danstruthers/hydra-16/reborn/docs/status.md

# Status

Where HydraOS (the rebuild, released as 1.0 at parity) stands against the plan's phases
([design/reimplementation-from-scratch.md](design/reimplementation-from-scratch.md), Part III), what the
spikes measured, and what measuring changed.  HyForth's, from step 6.6 on: [forth-status.md](forth-status.md).
The documentation (the plan's 19.4, written after the review of October 2026): [hydra-16.md](hydra-16.md), the guide
to the whole system, hardware and software (and `hydra-16.pdf`, the guide, the tutorial, the guides, the programmer's guide and the hardware reference as one book, to print);
[tutorial.md](tutorial.md), the first hour; [using/](using/README.md), the guides (rc, the tools, HyForth, hylang, BASIC); [programming/](programming/README.md),
the programmer's guide (calls, memory, tasks and notes, files and namespaces, servers and drivers, modules, video).
BASIC's design: [basic.md](basic.md).

## In short

HydraOS 1.0 is the parity release (October 2026: the user's word, on the emulator's evidence; the board's day of use is to come), the old system frozen in `old/` beside it.  Phases 0 to 2 and 4 to 7 are done, and phase 9's three tools; phase 3 (storage) is done but for the progress a long format or check shows, and phase 8 (the Vera X) but for its rest (8.8); phase 10 (the X16 migration utility) waits for the end.  Phase 4 (programs) is its loader, rc, the core tools, the assembly SDK, the C target and `ed`;
phase 5 (the remaining devices) is sound, the song player, GPIO and I2C, the clock, `/pc`, `xmodem`, and `/proc`'s files for a task's memory and state; phase 6 (HyForth) is `forth`, a Forth 2012 system (Core, Core Extension, Exception, Facility, File Access, Programming-Tools, Search-Order and String) that passes the Forth 2012 test suite's tests of them, with a `sys-` word for each system call a program makes (made from the specification), `SH`, `RUN`, banks and segments, Ctrl-C, libraries from `/lib/forth` and scripts (`forth file.fs`, `#!/bin/forth`); its ROM core is the Core word set, and the other word sets are pre-compiled libraries it loads into its dictionary (`/lib/forth/startup.fs` names those it starts with), and the login shell (`forth -l`: the ROM's `/lib/shell`).  Phase 7 (hylang) was done twice: the first hylang (7.1 to 7.4a, its library modules and its built-ins partially applied, to commit `a0973eb`) was deleted after a review of danlang and of it.  danlang, the reference, was fixed first (its 22 bugs, its quirks, one rule for each inconsistency, its shorthand made seven prefixes and `[...]`, callable hashes, text as bytes, one argument convention for its built-ins, and `reference.md`, its specification), and hylang was written again from scratch to the plan the review led to (`docs/hylang.md`): danlang's suite passes, the Hydra's layers are there (its built-ins, a `sys-` function for every call, the device libraries, hylang as a shell), and a bytecode machine and native code make it 1.9 times HyForth's time over twenty benchmarks.  Beyond the plan, BASIC: first EhyBASIC (Microsoft BASIC 2A) as a program, now a structured BASIC of the system's own in its place, in QuickBASIC's way on the Hydra's exact numbers (compiled whole into a stack machine's code; procedures, records, files, sound, graphics, system calls, a prompt that keeps a program, and a shell mode, `basic -l`).  The kernel boots in the emulator, runs POST (with the old
hardware test a key away), starts its modules from the paged ROM in tasks of their own, schedules them
preemptively, runs calls between tasks and copies between them, takes every interrupt through one path, manages
task RAM, banks and shared segments, and delivers notes.  The file layer is in: fds, channels, requests to
servers, servers built on srvlib, waits that a server's interrupt can end for a few cycles; and namespaces, Plan 9's:
binds, mounts, unions and union directories, a current directory, shared by a task's children till they change
them.  The console driver (`cons`, task F) serves `#c`: windows, Plan 9's way (rio's, on the serial terminal: a
console each, shown with Ctrl-] and a digit; each window's screen kept in the console driver's RAM banks, written
by a VT100 and painted from: the text windows' W1), lines edited at the console, raw keys,
Ctrl-C and Ctrl-\ to the shown window's note group, and paced sending up to 115200.  The kernel's own devices are a driver of
their own (`kdev`): the root's mount points, null and zero, the kernel's messages (`/dev/kmesg`: what it printed on the
bring-up console, the boot's too, its last 4K, kept in the kernel task's RAM), the ticks, the modules, the tasks, pipes, and the
environment.  The storage driver (`storage`, task E) owns the SPI bus and the disks: `#S` (the SPI devices), `#d`
(SD cards, through a cache of their blocks; the ROM disk; the RAM disks), and HydraFS on them (`#f`, the old
system's, ported: the module's second bank).  The paged ROM holds the ROM disk's volume after the modules (`/rom`:
`romfs/`).  init starts the RAM disks, builds its namespace from `/rom/lib/namespace`, and runs the login shell (`/lib/shell`'s:
HyForth, `forth -l`; rc without one) in window 0 and in each window the user asks for (Ctrl-] c); each shell builds
its own namespace from the same file as it starts (Plan 9's `newns`), with its own area of the RAM disk at `/ram`,
then runs its profile (rc's `/rom/lib/profile`, HyForth's `/lib/forth/profile.fs`).  `SPAWN` takes a
path through the namespace: a module of the paged ROM (`#m`'s files, at `/bin` by `#m/bin`) runs in place, and a
program in a file (a RAM program: `sdk/asm/hyx2.cfg`) is read into its task's RAM at `$0800` by the task itself as
it starts.  rc is Plan 9's (lists, quoting, `if`, `for`, `while`, `switch`, functions, redirections, pipelines,
background tasks, `$status`, globbing, `rc -c`), with the core tools beside it: files (`ls -l`, `cp -r`, `mv`,
`rm -r`, `du`, `df` ...), text (`wc`, `head`, `tail`, `uniq`, `xd`, `more` ...), tasks (`ps`, `kill`, `top`, `ns`
...), and the disks' (`mkfs`, `fsck`, `label`: RAM programs on the ROM disk, at `/bin` too).  Programs are written in
assembly (`sdk/asm`) or in C (`sdk/c`: cc65, with a library of the Hydra's own under the standard one: files,
buffered stdio, the environment, `system`, `signal` over notes, conio on the console's raw mode); `grep` and
`sort` are C programs.  `ed` is the old system's line editor, a program now (`edit` till phase 9's screen editor took the name).  The sound driver (`snd`, task C) serves the
YM2151 at `#a` (`/dev/snd`, `sndctl`, `bell`), with the old system's library (patches, notes, volumes, drums,
claims), and `sndctl` takes each channel's command as text, so rc makes sound; the console rings its bell; `play`
plays songs (the X16's ZSM files, on the ROM disk at `/rom/songs`) and scores (the score language, compiled as they
play), and a line of it (`play -m`) for each language's `snd-mml` and BASIC's `PLAY`.  The VIA's port A is `/dev/gpio` (its
pins, CA1 and CA2) and `/dev/i2c` (the I2C bus on two of its pins).  The clock is set from the DS1747 as the
system starts, if there's one: `/dev/time`, and `date`.  A folder on the PC is `/pc` (`#P`, the console driver's),
served over the serial line by the PC tool (`sim/tools/hydrapc.js`, which is the terminal too); `xmodem` sends
and receives a file with any terminal program.  `/proc/N` has a task's memory as files (`mem`, its 64K as it sees it,
and `ram`, its banks), its registers (`regs`), its environment (`env`), and a file to send it a note (`note`).
Phase 8 is the Vera X (the X16's VERA in slot 0: the user's is Joe Burks's VERA X, the X16 gateware):
the emulator has one (`sim/lib/vera.js`, `run.js --vera`, a live view in a browser), a driver serves it (`vid`: `#v`,
`/dev/vid`'s `ctl`, `term`, `vram`, `pal`, `sprites`, `font`, `frame` and `psg`, and claims for a program that
writes the chip itself), the console's windows are shown on its screen as well as the serial terminal (consctl's
`screen`, `serial`, `both`), its PSG is sound channels 8-23 (`/dev/snd`'s, `/dev/sndctl`'s `wave`,
`/dev/psg`; `play` plays a ZSM's PSG part), and its PCM plays samples (`/dev/vid/pcm` and `pcmctl`; `play`
plays WAV files and a ZSM's PCM instruments); the emulator plays its sound (`run.js --sound`, `--wav`); its keyboard
and mouse are its input controller's, the X16's SMC (the `input` program types the keys into the console, and the
mouse is `/dev/vid/mouse`, a sprite its pointer); the driver draws on its bitmap (`/dev/vid/draw`), with the same
words in each language (HyForth's `lib video`, hylang's `video`, C's `vera.h`, cc65's TGI); its SD card is a disk (`/sd/v`); the carrier card is
still to come (8.8).
Phase 9's tools are done: the debugger, `db` (`/rom/bin`, in C), starts a program stopped or stops a task, steps it an
instruction at a time (the kernel's `TASKSTEP`, behind `/proc/N/ctl`), runs it to breakpoints, and shows its
registers, code and memory with ld65's symbols; `edit` is a screen editor, nano's way, its text in RAM banks
(the old line editor is `ed` now); and `as` assembles ca65's language on the Hydra itself, the SDK's include files
in `/lib/as`, into the same program ca65 and ld65 make.

```
PASS boot    the kernel boots, POST finds nothing wrong; init runs hello and waits for it  (0 checks, 7.2M cycles)
PASS init    init from files (rc the shell, a card's /lib/shell naming it): the RAM disks started, the namespace file run, each shell's own namespace and /ram (a window's too); the shared RAM disk stopped, /bin's union still there  (0 checks, 32.0M cycles)
PASS newns   the default namespace's library (nslib): an old area emptied, a namespace file run (quotes, comments, $task, flags, bad lines)  (13 checks, 8.0M cycles)
PASS post-t  POST: a T line stuck low (U7)  (0 checks, 0.8M cycles)
PASS post-zp POST: only the zero page and stack per task (a decoding fault)  (0 checks, 0.8M cycles)
PASS post-ram POST: an address line of RAM module 1 stuck low; the module is left unused  (0 checks, 1.0M cycles)
PASS post-sh POST: no shared RAM  (0 checks, 1.0M cycles)
PASS hwtest  a T typed during POST starts the hardware test (paged ROM bank 1)  (0 checks, 1.0M cycles)
PASS hwtool  hwtest at rc: the system starts again (REBOOT), and POST takes REBOOT_HWTEST's word as a T  (0 checks, 12.6M cycles)
PASS task    tasks and the scheduler: SPAWN, EXITS, WAIT, SLEEP, preemption, PAUSE and WAKE, orphans  (29 checks, 8.2M cycles)
PASS note    notes: the defaults, handlers, a note to oneself, WAIT ended by one, note groups  (29 checks, 7.2M cycles)
PASS file    files and servers: OPEN, READ, WRITE, SEEK, STAT, DUP; text, ctl, data, directories; waiting  (54 checks, 10.0M cycles)
PASS ns      namespaces: BIND, MOUNT, UNMOUNT, unions and union directories, CHDIR, clean names, inheritance  (45 checks, 21.2M cycles)
PASS dev     the kernel's devices (kdev): #/, #n, #t, #m, #p; pipes; a union keeping what was there  (42 checks, 8.8M cycles)
PASS proc    /proc/N's mem (its RAM, bank, ROMs, the I/O area), ram (its banks), regs, env, note and fd (FD2PATH, TR_FD); ctl's stop and start; the kernel task's and a driver's refused  (46 checks, 9.4M cycles)
PASS forth   HyForth (Forth 2012): the test suite (Core, Core Extension, Double-Number, Exception, Facility, File Access, Locals, Memory-Allocation, Programming-Tools, Search-Order, String, Block) in three sessions, its files INCLUDED from a card, the word sets' libraries REQUIREd from /lib/forth; scripts (forth file.fs, #!/bin/forth: arguments, REQUIRE from /lib/forth, a library, an error, a pipeline, code banks); at the console: startup.fs's Programming-Tools (.S), libraries REQUIREd (and again after a MARKER), a definition, KEY? and KEY, errors (a file's, the system's), SH, RUN, a sys- word, a bank, the constants library, Ctrl-C, BYE  (3 checks, 513.8M cycles)
PASS basic   BASIC (docs/using/basic.md) at the console: its prompt, PRINT, exact numbers, keywords in either case, a program typed by its line numbers (LIST, RUN; GOSUB, DATA, READ, INPUT, DIM, a FUNCTION), Ctrl-C (Break in) in a GOTO's loop and CONT, INKEY$'s key, errors (at the prompt; a typed program's by its line's number), BYE (code 0); a pipeline into it (no prompt; an error's line ended, its end at stdin's); in /ram: SAVE, LOAD, RUN "name", a file not there (by its name), the text cat; scripts (basic file, #!/bin/basic: status 0 and 1, a file not there); files: OPEN's modes, PRINT #, INPUT #, LINE INPUT #, EOF, APPEND, CLOSE, the cat; a file not open, open, not there; INPUT's Redo from start; sound: SOUND's notes (a patch, a volume, off), SLEEP between them (timed), BEEP (the bell), a line for /dev/sndctl (the volume kept; the driver's error), a channel past 23, a patch past 127; SYS: calls by name (GETPID, TICKS, BANKS_ALLOC; one not there) and RREG; memory: FRE, an array of 10001, 301 strings; the shell (basic -l at rc's prompt): BASIC's lines and rc's by the rule, cd and the prompt, $status, %, a usage, ENV$, a program line, exit  (3 checks, 132.2M cycles)
PASS bsuite  BASIC's suite (tests/basic, docs/using/basic.md), from a card: programs that check themselves, each its checks and none failed (arithmetic: the operators and their order, exact numbers, complex numbers, literals: E notation, &H, the # forms, .5; suffixes; a base; the number functions: exact when they can be, else DIGITS digits, RND, fractions' and complex numbers' parts, GCD, FIB, shifts, VAL, STR$ in a base, MKN$; comparisons, the bitwise operators on big integers, IF's forms, SELECT CASE; strings: their functions, MID$ =, fixed lengths, past 255, the garbage collector; arrays: TO, dimensions, used before DIM, REDIM PRESERVE, ERASE, LBOUND, SWAP; FOR's exact steps, DO, WHILE, EXIT, GOTO, GOSUB, RETURN label, ON, line numbers, _; SUBs and FUNCTIONs: by reference and by value, recursion, STATIC, SHARED, CONST, a call among a call's arguments, one calling another, INCLUDE; TYPE: nested records, arrays of them, copies, a field by reference; DATA, READ, RESTORE, CONST, OPTION BASE, DEFSTR; ON ERROR, RESUME's forms, ERR, ERL, ERR$, the system's errors; files: OPEN's modes, PRINT #, WRITE #, INPUT #, LINE INPUT #, INPUT$, LOF, LOC, SEEK, GET, PUT, FREEFILE, directories; the Hydra's: SYS and RREG, a bank of its own, machine code, FRE, SLEEP, TIMER, DATE$, TIME$, ENV$, ARG$, COMMAND$, SHELL, SHELL$, STATUS; inline assembly: ASM blocks, CALL ASM's labels and registers, the program's variables and CONSTs by name, data, a block in a SUB, a later block's label, a macro, .if, cheap and unnamed labels, .include and a system call, the blocks' own bank and .bss); scripts piped into basic, their output tests/basic's: the errors' messages (at the prompt, a typed program's by its line numbers; ASM's: the assembler's at its line, a label not there, a block not ended, past 8K, ASM at the prompt; CALL ASM at the prompt), PRINT's layout (zones, TAB, SPC, POS, numbers' forms, PRINT USING's pictures and {} fields, WRITE, a base), the prompt (lines typed, replaced, taken out; LIST's ranges, labels; DELETE, CLEAR, SAVE, LOAD, RUN "f", STOP, CONT, SYSTEM), INPUT's answers (Redo from start, quotes, an empty line, LINE INPUT, INPUT ;)  (3 checks, 256.0M cycles)
PASS hyforth HyForth's additions (docs/hyforth.md): names in lower case; words (each word's xt, and whether it's a literal, immediate, assembly or Forth); the libraries loaded (libs), one not searched (-lib) and searched again (lib, where it was), the one with lib refused, a .fs one, one a MARKER takes out; disasm (the modes, the Rockwell opcodes, a jsr to a word), see of a code word (with disasm.fl, and without), sys, the bit words, random's numbers; the terminal's sequences, form, ekey and the keys (an arrow key, a character); the sound words (notes on the YM2151, a claim, the volume; a channel's level, its old name; the registers read back: a note's key code and fraction; a song by play, its error; a note by its frequency, a glide, the LFO, a channel's sensitivity, the noise; a line of MML and a chord, by play); ctl (and its error); compile-only words typed (THROW -14: >r, if, .", a synonym of one, a library's) and compiled  (3 checks, 172.0M cycles)
PASS fshell  HyForth as a shell (forth -l, shell.fl): its namespace and profile; a line Forth's or rc's by its first word (a number, a word, a pipeline, a redirection), or rc's by % (a program a word shadows); cd and the prompt (its format); a definition over lines (the second prompt); status and $status; & ($apid) and wait; programs as values: sh-out, output-of, a word's output a program's input (|, piped: one that ends first, Ctrl-C), spawn; Ctrl-C ending a program; errors, a usage; -lib shell and lib shell; exit  (3 checks, 74.8M cycles)
PASS fhydra  HyForth's Hydra words (hylang's layer 2): argc under forth -l (0: -l isn't an argument); a directory read (open-dir, read-dir, close-dir), =mkdir, get-dir and set-dir (the prompt follows), ior>text; setenv, getenv, unsetenv; a note to itself taken by on-note's handler, between words and in a loop, and one it says no to (as Ctrl-C); pause  (3 checks, 34.6M cycles)
PASS fdev    HyForth's device libraries (hylang's layer 3, source over the devices' files): gpio (pins, the port, ctl, CA1's edge), i2c (a memory written and read at a register, the devices), spi (an echo device's transactions, mode 3), cons (the window, the windows), proc (a task's args, cwd, regs, memory), clock (the chip, the time set), disk (a disk's ctl, the cards: one on SPI device 5), pc (the PC tool answers; a file of its read), and sound's note-of and tune (its notes on the YM2151, in time)  (3 checks, 231.0M cycles)
PASS findex  HyForth's index of the word lists (a bank's chains by a name's hash): a word redefined, a definition hidden till ;, a MARKER's words gone, MARKERs till the bank's full (started again), more word lists than records, EVALUATE of a bank's text (no index), the index's bank overwritten (started again); 500 searches of a name that isn't there in under 150 ticks (620 without the index)  (3 checks, 37.2M cycles)
PASS wcache  HydraFS's walk cache (the names looked up, there or not, and the directories' entries on the way): a name not there, then made, renamed, removed; directories made, removed, renamed under a name looked up; a name made through /lib's union after it wasn't there; each looked up again as it is now  (3 checks, 35.6M cycles)
PASS fload   HyForth loading a file: its read-ahead (a CR LF across its 512-byte buffers, CR LF and CR line ends, a line of 130 cut at 128, a last line ended by a CR and the file's end), names between tabs, numbers with each prefix, in base 36, a double; hydra.fs REQUIREd in under 300 ticks (383 before 6.20)  (3 checks, 25.2M cycles)
PASS fnumbers HyForth's numbers (numbers.fl, on the numbers and math libraries): numberstest.fth, each number word checked as the test suite checks (tester.fr's T{ ... -> ... }T): literals of every kind (and cells and doubles Forth's still), compiled with code banks and without, the number stack, the arithmetic, the tests, the conversions, the bits, text in the base and in others (set-base: cells read and shown by the library), the math functions, digits, the errors, nvariable, nconstant, nvalue; then n., n.base, n.s, nformat and cells in bases that aren't a radix, typed  (3 checks, 28.8M cycles)
PASS lshell  the shell /lib/shell names (the ROM's: /bin/forth -l, HyForth the login shell): init's in window 0, wstart's in a window made (Ctrl-] c: $window); send, a line typed in another window (#cN/kbdin), run there, then one longer than its keys' queue (the write waiting for room)  (0 checks, 29.8M cycles)
PASS spi     SPI and #S (storage): transactions, kept bytes, modes 0 and 3, one open at a time, the time a byte takes  (43 checks, 8.2M cycles)
PASS disk    the disks (storage): #d, the ROM disk, SD cards (SDHC and SDSC), RAM disks, their ctl files, the time a byte takes  (67 checks, 16.0M cycles)
PASS fs      HydraFS (#f): files and directories, create, write, holes, remove, rename, a length, format, label, check, old cards, mounts  (92 checks, 66.2M cycles)
PASS rom     the ROM disk: /rom (#f, spec x) walked on the Hydra, every file read back against its source (romfs/romfs.txt)  (2 checks, 285.6M cycles)
PASS load    SPAWN by path and the loader: modules in place (#m/bin), RAM programs from a card (arguments, fd maps), errors  (49 checks, 28.2M cycles)
PASS env     environments: ENV_GET, ENV_PUT, ENV_DEL, ENV_NAME, a child's copy, #e (/env) as files  (62 checks, 13.2M cycles)
PASS kmesg   the kernel's messages: KMESG (the boot's banner first, at offsets, the ring full: its last KMESG_SIZE) and /dev/kmesg (kdev's #n/kmesg) read in parts  (12 checks, 21.2M cycles)
PASS rc      rc: quoting, lists, redirections, pipelines, if, for, while, switch, functions, globs, scripts, Ctrl-C, its start  (3 checks, 87.8M cycles)
PASS tools   the core tools at rc: files, text, tasks, the disks' (/rom/bin); /proc's args, cwd, ns; the SDK's samples  (3 checks, 156.0M cycles)
PASS c       the C target (cc65): its samples at rc, the library's test (ctest), conio's raw keys (an Escape alone too; and raw ended with the program)  (81 checks, 89.4M cycles)
PASS cnum    the numbers in C and assembly: num.h's test (ntest: the number libraries from C, printf's and scanf's %N and %{base}), calc at rc (its operators, functions, bases, digits, errors, its input a line at a time, long results), the assembly sample nsum (numbers.inc, numlib.s)  (65 checks, 76.6M cycles)
PASS race    the race sample (sdk/c/samples/race: tasks sharing a segment) at rc: four tasks each add 1 to a counter 300 times (a read, some work, a write); with nothing to keep them apart adds are lost, with a mutex none; the barrier (ready and go)  (3 checks, 40.8M cycles)
PASS chorus  the chorus sample (sdk/c/samples/chorus: the console shared) at rc: four tasks sing a line each, a letter at a time; with nothing between them the letters tangle; with a mutex each line is whole (in the order they took it); with a baton (a semaphore each, passed round) whole and in turn  (3 checks, 39.8M cycles)
PASS philo   the philo sample (sdk/c/samples/philo: the dining philosophers, each fork a mutex, a shared segment) at rc: five tasks eat three meals each, the lower-numbered fork first, none in two hands at once; then -d, each its left fork first: a deadlock, seen, and ended (the tasks killed, their mutexes given back); then under rc -c, Ctrl-C: philo's handler ends it, rc -c waiting for it (then ending, before its next command)  (3 checks, 77.2M cycles)
PASS prodcons the prodcons sample (sdk/c/samples/prodcons: counting semaphores and a mutex, a ring in a shared segment) at rc: two producers make 20 items each, two consumers use them, each once; the producers waited for room, and the consumers for items  (3 checks, 31.2M cycles)
PASS round   the round sample (sdk/c/samples/round: a barrier, then each task its own time) at rc: four tasks sing a round on YM2151 channels 0-3, an eighth 12 ticks; each voice's 27 notes in time (hy_sleep_until: within 5 ticks), each voice two bars after the one before  (3 checks, 38.0M cycles)
PASS ed      ed, the line editor: a file made, printed, changed and written; its errors; q twice; Ctrl-C at its prompt; w name  (3 checks, 23.6M cycles)
PASS edit    edit, the screen editor (/rom/bin/edit, its text in RAM banks): a file typed and saved; a line cut and pasted; o replaced with 0, all; a cut undone; a line copied into a second file; a CR LF file kept so; a 20K file (several blocks) cut, pasted and saved  (3 checks, 174.0M cycles)
PASS as      as, the assembler (the module as): the SDK's hi from /lib/as, with its include files there, the same bytes as the build's (ca65 and ld65), run, its labels file (-l); nsum (numbers.inc's macros, numlib.s) the same; t_asall (tests/ram: every opcode in each mode, directives, expressions, labels, macros, conditionals, segments, .include, .incbin) the same as the build's; -b with .org; errors with their files and lines; a warning  (3 checks, 105.0M cycles)
PASS dis     dis, the disassembler (/rom/bin/dis: as's inverse, the asm library's instructions): the SDK's tick as as's source (its code followed from main, its labels, hydra.inc's calls and registers, its data and BSS); sources that as assembles to the same bytes: hi with its labels (as -l), upper in the SDK's columns (-w), db (C, 20K) with ld65's labels, every opcode (three operands each) raw from an address (-c -o); its usage and a file not a program  (3 checks, 1214.0M cycles)
PASS sound   the simulator's sound (sim/lib/audio.js: run.js --sound, --wav), at rc: the YM2151's (opm.js, ymfm's) A4 on channel 4, then the Vera X's PSG's A5 on a sawtooth (channel 8), each heard at its pitch; the stream 48,000 samples a second of the Hydra's time  (3 checks, 24.2M cycles)
PASS snd     sound (#a): snd, sndctl and bell; the volume, claims (one another program holds), the shadow, tones (C, snd.h); sndctl's channel commands as text (patch, note, level and vol, pan by word and number, bend below 0, off, drum, reg: their registers on the chip; a channel another program has; numbers out of range, or missing); freq (a note by its frequency, its 64ths), glide, lfo, sens, noise  (3 checks, 81.4M cycles)
PASS mml     scores (play's, modules/play/mml.inc: hysong.js's language compiled as it plays): play -o's ZSM of the old test song (every channel, algorithm and LFO waveform, noise, slides, legato, drums, repeats, the timers) and of scom, each the same as hysong.js's byte for byte; scom played as a score and as hysong.js's ZSM, the chip's writes the same, in the same order, and in time; play -m (a line on a channel, its own instrument), -c (a chord, a note a channel), -x (the X16's MML: T, upper-case notes, S0 legato, K), I (a patch by number); a score's errors, the lines'  (3 checks, 228.6M cycles)
PASS play    the song player: its errors; a song timed (its key-ons against its stream), its channels claimed and given back; scom; jukebox  (3 checks, 50.4M cycles)
PASS gpio    GPIO (#g) and I2C (#i): CA1's edges (its own line), pins, the port, ctl; the I2C bus, a memory written and read  (3 checks, 62.6M cycles)
PASS clock   the clock: from a DS1747 at its start, /dev/time and date, the calendar (month ends, leap years), the chip set, stamps  (3 checks, 36.0M cycles)
PASS pc      /pc (#P, the console driver's): a folder on the PC through the serial port, its frames between the console's bytes; files read, made, copied, renamed, removed; a program run from it  (3 checks, 89.2M cycles)
PASS pc-two  /pc from two tasks at once (a pipeline: one reads a file, the other writes its copy): one request at a time, the other waiting its turn  (3 checks, 114.4M cycles)
PASS pc-fast /pc at 115200: a file copied on the PC through the Hydra and compared, no reply's byte lost (none asked for again: the ACIA's interrupt goes ahead of the tick's and timer 2's)  (3 checks, 74.0M cycles)
PASS pc-song a song played from /pc (play /pc/t.zsm 2), its loop twice more, in time: a read on the line doesn't hold a note up  (3 checks, 22.0M cycles)
PASS pc-ro   /pc served read-only (the PC tool's --read-only): files read; a write, a create, a remove, a mkdir, a rename refused; the folder as it was  (3 checks, 25.0M cycles)
PASS pc-none /pc with no PC tool: the attach (its bytes on the terminal) unanswered, an error a second on, each time; the console goes on  (3 checks, 19.4M cycles)
PASS pc-damage /pc's frames damaged on the line: requests (the PC tool asks for them again: its NAK), a reply (the Hydra asks again, and the PC tool answers from its last reply); the answers right, nothing damaged shown  (3 checks, 17.6M cycles)
PASS xmodem  xmodem: a file received (1K blocks, a CRC; one damaged, one sent twice) and sent back (128-byte blocks, a checksum, one NAKed; 1K ones), the same; Ctrl-C at its start; the PC cancelling; 115200  (3 checks, 89.6M cycles)
PASS cons    the console: lines, editing, history, raw keys, its answers (DA, CPR, DECRQM, the size, DECREPTPARM), the window's size (the terminal's report typed, terminal size, KEY_RESIZE, the terminal asked), keys vt (DECCKM, VT52 mode), Ctrl-C, windows (shown, repainted, made, gone), groups (Ctrl-] c's, new's, new group's; Ctrl-] Tab, Ctrl-Tab, Ctrl-Shift-Tab, Ctrl-] n and p; KEY_FOCUS), 115200, the bell  (238 checks, 81.6M cycles)
PASS mem     memory: BREAK, pages, banks, a shared segment between tasks (and kcopy from it); #r (raw RAM, init's); #s (a segment by name)  (46 checks, 9.8M cycles)
PASS sem     semaphores: counts and mutexes, waits ended by a release, a free and a note, a task's end; GETPPID  (36 checks, 8.8M cycles)
PASS xcall   XCALL: a library module's routines (t_lib), registers and flags both ways, its bank and back, a system call from it  (9 checks, 4.2M cycles)
PASS numbers the numbers library (modules/numbers): its calls as a card's file has them (tests/numtest.js), each checked against the reference (sim/tools/numfmt.js), and to keep the caller's bank, zero page and r0-r3  (6 checks, 1174.2M cycles)
PASS step    the debugger's steps (TASKSTEP, /proc/N/ctl): a program started stopped (SPAWN_STOPPED), each kind of instruction a step at a time (out of line, or on its frame), a JSR stepped over, a breakpoint, a program's own BRK; refused steps  (65 checks, 10.6M cycles)
PASS db      the debugger at rc (/rom/bin/db): the SDK's hi started stopped, its labels from /pc (ld65's) and hydra.inc's calls and registers, registers, steps, a disassembly (as as writes it: the asm library's, symbols in the operands), a breakpoint hit twice, a JSR to the kernel stepped over, until, memory read and written, and on to its end  (3 checks, 60.2M cycles)
PASS banks   a module of two banks: calls between them (FAR2, FAR1), registers and C, each bank's data  (6 checks, 3.6M cycles)
PASS banks3  a module of three banks: calls from any bank to any (FARN), registers and C, each bank's data, each bank set again  (7 checks, 3.6M cycles)
PASS scall   spike S3: calls into a driver's task, its errors, a busy driver, the round trip  (12 checks, 4.0M cycles)
PASS heap    hylang's runtime (modules/hylang/heap.inc, phase 1): values and fixnums, cells, symbols and atoms, strings; the collector (a list kept while garbage is taken back, a structure deeper than the mark stack, blobs dropped and the rest moved down); the heap growing, a million cells made and dropped with none lost, and its end (E_NOMEM)  (49 checks, 506.4M cycles)
PASS hylang  hylang's REPL, evaluator, built-ins, numbers, strings, hashes, streams and system library (phases 3 to 7): the reader's every form (in Q-expressions, printed as they're read) and its errors, an expression over lines, 255 brackets open; lines evaluated: def, fn, fun, recursion 1,000 deep (2,500 the most: deeper, an error), a tail loop, errors, partial application, too many arguments, &_, let, the loops, output-of, try, map, format, + of strings, cmp, closures, fexprs; numbers past a fixnum, fractions, fixed decimals and complex numbers, read in bases and written in them, to-fixed, truncate, fib, random, the bits; the string built-ins; hashes (made with their values evaluated, called, a method with &0, a private entry, a locked hash, cloned, listed); read, the clock, rc's lines run (their output, their exit status), print-to and write-to stdout, save, the environment, a system error's code; filter, the folds, any?, all?, find, count, sum, product, sort (by cmp, by a function, its error), subset, index-of, gensym, to-atom, random; Ctrl-C at the prompt and in a loop; (exit 3); stdin a pipe, its end; hylang -g (a collection before every allocation)  (3 checks, 676.8M cycles)
PASS hysuite1 hylang's suite, part 1 of 5: danlang's run.dl with reader.dl, eval1.dl, eval2.dl (run.dl a script, args its name, its status; with its harness, loaded from a card: load reads a file an item at a time, refilled as it goes; a load nested in another)  (3 checks, 365.0M cycles)
PASS hysuite2 hylang's suite, part 2 of 5: danlang's run.dl with eval3.dl  (3 checks, 351.0M cycles)
PASS hysuite3 hylang's suite, part 3 of 5: danlang's run.dl with eval4.dl  (3 checks, 364.0M cycles)
PASS hysuite4 hylang's suite, part 4 of 5: danlang's run.dl with eval5.dl  (3 checks, 508.4M cycles)
PASS hysuite5 hylang's suite, part 5 of 5: danlang's run.dl with eval6.dl, scope.dl, control.dl, errors.dl, lists.dl, strings.dl, numbers.dl, math.dl, hashes.dl, types.dl, io.dl, system.dl, bits.dl, buffers.dl, library.dl (danlang's library, hylang's from its snapshot (globals.dl) and the ROM disk's /lib/hylang (dice.dl and screen.dl, where load finds a bare name, and use); files written on the card, programs run, the clock a DS1747's)  (3 checks, 361.2M cycles)
PASS hytext  hylang without its snapshot (a ROM without the module hysnap): its library loaded as text as it starts (/lib/hylang/globals.hl, the ROM disk's), the same banner, the library's definitions there; a tail loop of 50,000 steps  (3 checks, 361.0M cycles)
PASS hyspeed hylang's budgets (phase 8's, at 3.58 MHz, its library loaded): a parameter looked up, a call of a function of two arguments, a tail loop's step (if, zero?, -, the call), map with a function of one argument, an item; each the difference of two lines' times, from the echo to the value  (3 checks, 45.0M cycles)
PASS hyhydra hylang's Hydra built-ins and system calls (the plan's phases 9 and 10): hydra.hl as a script (sysinfo, mods, errstr; ps, task-info, yield, sleep-until; peek and poke, the task's banks, a shared segment, free; bind, mount, unmount, ns, newns; note, on-note; hold; key?; sys- functions of each group of calls, and their errors), and again with a collection before every allocation (sys- names bound, the calls' values made, puts and putc); at the prompt, raw keys (key: a character, the terminal's up key; key?) and Ctrl-C given to on-note's function  (3 checks, 1664.6M cycles)
PASS hysh    hylang as the shell (the plan's phase 12: hylang -l, login.hl, profile.hl, shell.hl): the rc test's lines that stand alone, each an rc line at hylang's prompt (rc -c), as at rc's; hylang's lines by their first character; cd and the prompt; $status and status; bind and unmount in hylang's namespace; a usage; & and $apid; Ctrl-C to cat, rc's; exit  (3 checks, 176.4M cycles)
PASS hywin   hylang as a window's shell: a card's /lib/shell naming /bin/hylang -l, init's in window 0 and wstart's in a window made (Ctrl-] c: $window, cons.hl's window)  (0 checks, 86.2M cycles)
PASS bplay   BASIC's PLAY: a line of MML on channel 0 and on another (play -m), a score file (play name.mml), its time waited for (the program goes on after); play's error (its message as BASIC's, in its line; BASIC's status 1), a channel past 23 (illegal function call); SOUND's text commands (sndctl's: a note, a level)  (3 checks, 35.6M cycles)
PASS bawin   BASIC as a window's shell: a card's /lib/shell naming /bin/basic -l, init's in window 0 and wstart's in a window made (Ctrl-] c: $window, ENV$): the prompt, a BASIC line and an rc line in each  (0 checks, 17.8M cycles)
PASS bench   hylang's, HyForth's and BASIC's benchmarks (romfs/bench: bench.hl and hl/NAME.hl, bench.fs, bench.bas, and benchasm.bas, BASIC's inline assembly: all twenty in each; sim/bench.js times them against each other) at their quick sizes, all of hylang's in one hylang: each language's result of each the same (calls, fib, tak, ack; loop, while, dotimes, nested; gcd, collatz, hash; sieve, sort, matrix, queens; mapf, fold, each; chars, digits)  (3 checks, 164.0M cycles)
PASS hydev   hylang's device libraries (the plan's phase 11: /lib/hylang's, loaded by use, over the devices' files), devices.hl as a script: gpio (pins, the port, ctl as a hash, CA1's edge), i2c (a memory written and read at a register, the devices, one that doesn't answer), spi (an echo device's transactions, mode 3), cons (the window, the windows, the bell), proc (a task's args, cwd, regs, memory, banks; its environment, its namespace), clock (the chip, the time set), disk (the disks, the cards: this one and one on SPI device 5; the ROM disk's room), pc (the PC tool answers; a file of its read), snd (note-of; a tune, its notes on the YM2151 in time; a channel's settings; the registers read back: a bent note's key code and fraction; a frequency, a glide, the LFO, a sensitivity, the noise; a line of MML and a chord, by play)  (3 checks, 207.0M cycles)
PASS kcopy   spike S2: copying between tasks  (6 checks, 5.0M cycles)
PASS irq     spike S1: 115200 received by an irq entry while tasks spin  (6 checks, 2.6M cycles)
PASS vera    the emulator's Vera X (sim/lib/vera.js), the chip as a program sees it (no vid): the version register; ADDR0 and ADDR1, their steps, a data port's byte fetched ahead; the display's registers at the start; VSYNC (59.5 a second), LINE and SCANLINE (bit 8 too); sprites colliding; the PCM FIFO (empty, full, AFLOW and its interrupt's time); a PSG voice; the SPI port with no card; FX (the cache's writes and fill, transparency, the multiplier, the line helper, the fill length); CTRL's reset  (60 checks, 16.0M cycles)
PASS vid     the Vera X's driver (vid: #v), through its files: ctl's state; the terminal (/term): text written and read back, a CSI move, a line erased, wrapping, BS and TAB, 70 lines scrolled, SGR's colours (in the map's cells), the cursor's sprite; /frame (a frame a read, 59.5 a second); /vram, /pal, /font, the files' lengths; ctl's commands (mode, cursor, border, bitmap, bad ones); claims: a write to the terminal E_BUSY meanwhile, shown after the release; claim all (the font back); another task's (E_BUSY), ended by its end  (73 checks, 14.2M cycles)
PASS vid-none vid with no card: its init looks for DETECT_TICKS, then ends; no #v (E_NODEV)  (1 checks, 2.6M cycles)
PASS screen  the console on the Vera X's screen (cons's second terminal: vid's /term), at rc: /dev/vid; consctl's terminal both, serial (the screen left as it was), both again (repainted); a font written to /dev/vid/font; ctl's output (NTSC, mono, 240p; VGA has neither); colours from a file (SGR, in the cells); DECSCNM (every cell reversed); the DEC graphics (ESC ( 0) as the font's glyphs; what rc shows, on the screen as on the serial port  (3 checks, 66.2M cycles)
PASS vt      the console's VT100 (W1): sequences into a window not shown, its /text read back: text, the cursor's moves, erasing, inserting and deleting, the scrolling region, the scrollback, tabs, autowrap, insert mode, the character sets, DECSC and origin mode, DECALN, RIS, REP, SGR, VT52 mode, the alternate screen, double width and height, sequences dropped, cancelled and split; each as sim/lib/vt.js has it, and vt.js as xterm.js has it (if it's installed)  (3 checks, 144.2M cycles)
PASS vtpaint a window painted (W1): text in colours, a box in DEC graphics, a line autowrapped, a double-width row, a region and the cursor, written into a window not shown, which is then shown: what the serial port's terminal shows (sim/lib/vt.js: its characters and colours) and what the screen shows, as the window has it  (3 checks, 49.2M cycles)
PASS vtjump  scroll jump (consctl): the ROM disk's api.md (38K) cat to the window shown, its writer not waiting for the serial line, the terminal painted as it can: far fewer bytes sent than written, the file's last line shown at the end; scroll smooth again  (3 checks, 37.2M cycles)
PASS vtsize  a window's size (W3: terminal size, both terminals on): a window not shown with 30 lines in it, made shorter (the cursor high: rows dropped at the bottom), taller (the scrollback's rows down onto it, then blank ones), narrower (the long lines cut), wider; its alternate screen in use, shorter (rows off its top dropped), then the main one again (the saved cursor where its row went); its /text after each, a mark at its cursor, as sim/lib/vt.js's resize has it  (3 checks, 56.4M cycles)
PASS vtmode  a window's size from the screen's (W3): the screen alone (80 x 60, less its chrome's 3 rows: the bar, the header, the footer), vid's mode changed under the console (40x30: its next write refused once, the size looked at, the windows resized and the screen painted again; 80x30), then both terminals (the smaller: the serial port's 80 x 24)  (3 checks, 33.4M cycles)
PASS vtedit  the line editor at the window's width (W3): rc's lines typed in a window 20 columns wide (terminal size 20 24), each longer than a row: Left back across the rows, characters inserted, Home, Right, Delete, End; then that line again (Up), cut back with Backspace across the rows; a third made 30 columns wide as it's typed (the terminal's report among the keys: the line drawn again), then edited: what rc read, and what the serial port's terminal shows of each line (sim/lib/vt.js, 20 and 30 columns), as typed, the rest of its last row blank  (3 checks, 25.4M cycles)
PASS winsize a window's size in each language (W3): terminal size 100 30, then rc (consctl's size line), HyForth (form, k-resize), hylang (cons.hl's window-size), C (conio: the keys sample's screensize, and CH_RESIZE as the terminal's report is typed, 120 x 40); the editor drawn again as its window changes (its help lines on the new last rows)  (3 checks, 53.8M cycles)
PASS winchrome the chrome on the screen (W4): its label (#c0/label, OSC 2, empty: its program's name), its status line (wctl's status, and DECSASD's, after DECSSDT 2), the header's and footer's formats (%p, %l, %n, %s, %c, %r, %m, %[7], %=), the bar (its defaults: the windows, the time; at the bottom; off), a window's chrome rows turned off (its size grows by each), activity in a window not shown (monitor on: +; a bell: !); read back from vid's screen  (3 checks, 65.0M cycles)
PASS winser  the chrome on the serial port (W4b: chrome serial on): its bar, header and footer drawn there, the window 80 x 21 below the bar and header (its margins sent offset); 25 lines scrolling the window's rows alone; a clear (ED 2) then the chrome drawn again; a CUP and DECSTBM from a program offset; chrome serial off (80 x 24 again): what the PC's terminal shows (sim/lib/vt.js)  (3 checks, 29.6M cycles)
PASS winwords the window's chrome in HyForth and hylang (W4c; C's are ctest's): window-label (read back from /dev/label; hylang's read too), window-status (the footer's %s, on the screen's footer row: both terminals on, the window 80 x 24 below the bar and header), window-ctl  (3 checks, 41.4M cycles)
PASS newwin  new-window (W5c): a command run in a window made and shown, in this one's group ($window its number; the window gone when it ends, this one shown again), -g's in a group of its own, the shell (/lib/shell's: HyForth) with none; HyForth's new-window and new-group, hylang's  (3 checks, 105.4M cycles)
PASS winkeys the windows' keys (W5d): wctl's key lines (the prefix Ctrl-A, keys after it, Ctrl-Tab's action; a digit, an unknown action, Ctrl-C as the prefix refused); Ctrl-] w's list (a line a window: its key, number, label and group; chosen with the arrows and Enter, a key, q, Escape twice; the window shown each time it opens marked; activity, +, as monitor on and off say); Ctrl-Tab and Ctrl-Shift-Tab as Windows Terminal's win32-input-mode sends them, made into CSI u's by sim/lib/win32in.js (the PC tool's --win32-input); keys mods (HyForth's ekey: Ctrl-Up, Up, Shift-F2, the k- masks or'd in)  (3 checks, 82.2M cycles)
PASS snarf   /dev/snarf (W6a): written and read back; a file through it, the same (cmp); 8K at most (past them, disk full); Ctrl-] y's paste into rc as its keys (two lines: each LF a CR); hylang's snarf! and snarf; bracketed paste (?2004) to a keys vt reader, HyForth's ekey: CSI 200 ~, the text, CSI 201 ~  (3 checks, 55.4M cycles)
PASS scrollview the scrollback's view (W6b): Ctrl-] [ (its end), PgUp, the arrows, Space's mark and Enter's copy (the lines marked to the cursor's, into /dev/snarf); Enter alone (the cursor's line); Escape twice; Shift-PgUp (a page up) while a program writes on (its output there after: the view left with q), Home and End; its footer's %y on the serial port (default chrome serial on)  (3 checks, 68.2M cycles)
PASS history a window's history (W6c: wctl's history N): 64 rows past its scrollback's, a hundred lines and more kept (/dev/text has them all: 105 lines, 64 without), the view's Home the oldest of them (copied into /dev/snarf, then a page down and back); history 0 (its rows gone: 64 lines again); history 200 refused  (3 checks, 57.4M cycles)
PASS tiles   tiles (W7a: wctl's layout): three windows of a group in rows (80 x 7 each on the serial port's 80 x 24, a header row each), columns (26 x 23, a border between), a grid (40 x 11, 39 x 11, the third 80 x 11), zoomed and back (Ctrl-] z: the focus alone, 80 x 24, the others keeping theirs), tabs; then rows again, the focus moved by Ctrl-] and the arrows and Ctrl-] Shift-Tab (back to window 0); the screen at the end: the three tiles, their headers (the focused one's reversed), each window's text in its tile  (3 checks, 121.6M cycles)
PASS tilesplit splits (W7a): Ctrl-] s, a window with a shell (wstart's, HyForth) below in the group, rows; a Forth line there; Ctrl-] Up back to window 0, its wctl (two windows, each 80 x 11: the serial port's tiles, the smaller); Ctrl-] v, a third; the Vera X's screen read back: the bar, then window 0's tile's header  (0 checks, 98.0M cycles)
PASS popups  popups (W7b: wctl's float X Y C R): window 1 floating at 20, 6 (30 x 8: its consctl's size), boxed, shown over window 0 as twelve lines are written there (painted around the box); Ctrl-] 0 and window 0 alone again; Ctrl-] ? (the keys, a popup: the bindings) and q; then the popup over the group's two tiles (rows: windows 0 and 2; window 1, floating, no tile), the screen at the end checked: the tiles' headers, the box, the text in each  (3 checks, 94.8M cycles)
PASS seats   seats (W8a: consctl's seats): the screen and the serial port each a seat; Ctrl-] c at the keyboard, a group of its own (wstart's shell) shown on the screen alone, sized to it, the serial port still showing window 0 (both marked in wctl); the keyboard's keys to it (its text read back from the serial port), its Ctrl-C a note to its shell, not window 0's; consctl reads terminal seats; both, one seat again (the screen showing window 0)  (0 checks, 93.8M cycles)
PASS winmouse the mouse in the windows (W8b): the input program's reports (CSI < B ; X ; Y M and m) to a program that asks for them (?1000, ?1006: HyForth's ekey, keys vt), at its own cell; a click in a tile not focused (Ctrl-] s's rows: window 0's, above) focuses it; the wheel over a window that doesn't ask, its scrollback's view (Enter: its cursor's line into /dev/snarf, the view left); the PC terminal's reports from the serial port (the console's ?1000 and ?1006 sent it as its window asks), its tile's cell (row 3, its header row 1: the window's 2)  (0 checks, 132.6M cycles)
PASS pcm     the Vera X's PCM (vid's /pcm and /pcmctl), at rc: its files and state; the rate (the VERA's nearest) and volume; raw samples from a card into the FIFO, drained; bad commands; /pcm one task's (another's pcmctl: busy); WAV files played (8 bits mono, made signed; 16 bits stereo past an odd chunk; a float one, not a song); a ZSM's PCM instruments (one, then one looped, stopped by the FIFO emptied: from RAM) and its claim of the PCM; one too big for RAM (from the file); the FIFO's bytes in order, none lost, its runs dry only at the ends  (3 checks, 75.8M cycles)
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
