danstruthers/hydra-16/reborn/tests/basic/arith.bas

' arith.bas - BASIC's numbers: exact integers of any size, fractions, fixed decimals, complex numbers; the
' operators and their order; literals (E notation, &H, the Hydra's # forms); a number's suffixes, one variable
DIM SHARED checks, failed
SUB ck (got, want, what$)
    checks = checks + 1
    IF got <> want THEN failed = failed + 1: PRINT "FAIL "; what$; ":"; got; "not"; want
END SUB

' The operators
ck 2 + 3, 5, "+"
ck 2 - 5, -3, "-"
ck 6 * 7, 42, "*"
ck 7 / 2, 3.5, "/"
ck 2 ^ 10, 1024, "^"
ck 7 \ 2, 3, "\"
ck -7 \ 2, -3, "\ toward 0"
ck 7 MOD 2, 1, "MOD"
ck -7 MOD 2, -1, "MOD's sign"
ck 7.6 \ 2.4, 4, "\ rounds first"
' Their order
ck 2 + 3 * 4, 14, "* before +"
ck (2 + 3) * 4, 20, "( )"
ck 2 * 3 ^ 2, 18, "^ before *"
ck 10 - 2 - 3, 5, "- from the left"
ck 100 / 10 / 2, 5, "/ from the left"
ck 2 ^ 3 ^ 2, 64, "^ from the left"
ck -2 ^ 2, -4, "- after ^"
ck 2 ^ -1, 1 / 2, "^ -"
ck 5 - -3, 8, "- -"
ck 2 * -3, -6, "* -"
ck 7 MOD 4 + 1, 4, "MOD before +"
ck 10 \ 3 * 2, 1, "\ after *"
ck 1 + 2 = 3, -1, "= after +"
' Exact
ck 0.1 + 0.2, 0.3, "0.1 + 0.2"
ck 1 / 3 + 1 / 3 + 1 / 3, 1, "thirds"
ck 10 / 4, 5 / 2, "a fraction"
ck 2 ^ 100, VAL("1267650600228229401496703205376"), "2 ^ 100"
ck 2 ^ 64 - 1, 18446744073709551615, "2 ^ 64 - 1"
ck (2 ^ 70) \ (2 ^ 60), 1024, "big \"
ck (10 ^ 30 + 7) MOD 10, 7, "big MOD"
ck 1.25 * 4, 5, "1.25 * 4"
ck 3 / 4 * 4, 3, "3 / 4 * 4"
ck 1 / 7 * 7, 1, "sevenths"
ck 0.5 ^ 2, 0.25, "0.5 ^ 2"
ck 4 ^ 0.5, 2, "4 ^ 0.5"
ck (9 / 4) ^ 0.5, 3 / 2, "(9/4) ^ 0.5"
' Complex numbers
ck (1 + 2i) * (1 - 2i), 5, "(1+2i)(1-2i)"
ck 2i * 2i, -4, "2i * 2i"
ck SQR(-4), 2i, "SQR(-4)"
ck (3 + 4i) - 4i, 3, "back to real"
' Literals
ck 1E3, 1000, "1E3"
ck 1.5E-2, 0.015, "1.5E-2"
ck 12.5E+1, 125, "12.5E+1"
ck 1D2, 100, "1D2"
ck &HFF, 255, "&HFF"
ck &hff, 255, "&hff"
ck &O17, 15, "&O17"
ck &B101, 5, "&B101"
ck #xFF, 255, "#xFF"
ck #b101, 5, "#b101"
ck #16r1F, 31, "#16r1F"
ck #b0.1, 1 / 2, "#b0.1"
ck .5, 1 / 2, ".5"
' A suffix: one variable, x and x% and x# the same
x = 5: ck x%, 5, "x%"
x# = 7: ck x, 7, "x#"
x! = 9: ck x&, 9, "x&"
DIM y AS INTEGER: y = 2.5: ck y, 2.5, "AS INTEGER: exact"
ck CINT(2.5), 2, "CINT a half to even"
ck CINT(3.5), 4, "CINT 3.5"
ck CINT(-2.5), -2, "CINT -2.5"
ck CLNG(7.5), 8, "CLNG"
ck CSNG(1 / 3), 1 / 3, "CSNG as it is"
ck CDBL(0.1), 0.1, "CDBL as it is"
' Numbers in a base
BASE "x"
ck 0FF, #d255, "BASE x: 0FF"
ck 10, #d16, "BASE x: 10"
BASE "d"
ck 10, 10, "BASE d again"
PRINT "arith:"; checks; "checks,"; failed; "failed"
